ZIOCC/Zio-Qwiic-E-ink-Display-2.9ich/Black & White/firmware/Arduino/QWIICGDE029A1.h

/*******************
QWIICGDE029A1,h

*******************/

#ifndef _QWIICGDE029A1_h
#define _QWIICGDE029A1_h


#include"Arduino.h"
#include <Wire.h>

const unsigned char F8x16[]PROGMEM={
0xFF,0xFF,0xFF,0xFF,0xFF,0xFF,0xFF,0xFF,0xFF,0xFF,0xFF,0xFF,0xFF,0xFF,0xFF,0xFF,/*" ",32*/

0xFF,0xFF,0xFF,0xF7,0xF7,0xF7,0xF7,0xF7,0xF7,0xF7,0xFF,0xFF,0xF7,0xF7,0xFF,0xFF,/*"!",33*/

0xFF,0xB7,0xDB,0xDB,0xED,0xFF,0xFF,0xFF,0xFF,0xFF,0xFF,0xFF,0xFF,0xFF,0xFF,0xFF,/*""",34*/

0xFF,0xFF,0xFF,0xB7,0xB7,0xB7,0x81,0xDB,0xDB,0xDB,0x81,0xDB,0xDB,0xDB,0xFF,0xFF,/*"#",35*/

0xFF,0xFF,0xEF,0xC3,0xAD,0xAD,0xED,0xE3,0xCF,0xAF,0xAF,0xAD,0xAD,0xC3,0xEF,0xEF,/*"$",36*/

0xFF,0xFF,0xFF,0xDD,0xDA,0xEA,0xEA,0xF2,0xD5,0xA7,0xAB,0xAB,0xAD,0xDD,0xFF,0xFF,/*"%",37*/

0xFF,0xFF,0xFF,0xF3,0xED,0xED,0xED,0xF5,0x89,0xDA,0xD6,0xE6,0x6E,0x91,0xFF,0xFF,/*"&",38*/

0xFF,0xF9,0xFB,0xFB,0xFD,0xFF,0xFF,0xFF,0xFF,0xFF,0xFF,0xFF,0xFF,0xFF,0xFF,0xFF,/*"'",39*/

0xFF,0xBF,0xDF,0xEF,0xEF,0xF7,0xF7,0xF7,0xF7,0xF7,0xF7,0xEF,0xEF,0xDF,0xBF,0xFF,/*"(",40*/

0xFF,0xFD,0xFB,0xF7,0xF7,0xEF,0xEF,0xEF,0xEF,0xEF,0xEF,0xF7,0xF7,0xFB,0xFD,0xFF,/*")",41*/

0xFF,0xFF,0xFF,0xFF,0xF7,0xF7,0x94,0xE3,0xE3,0x94,0xF7,0xF7,0xFF,0xFF,0xFF,0xFF,/*"*",42*/

0xFF,0xFF,0xFF,0xFF,0xFF,0xEF,0xEF,0xEF,0x01,0xEF,0xEF,0xEF,0xFF,0xFF,0xFF,0xFF,/*"+",43*/

0xFF,0xFF,0xFF,0xFF,0xFF,0xFF,0xFF,0xFF,0xFF,0xFF,0xFF,0xFF,0xF9,0xFB,0xFB,0xFD,/*",",44*/

0xFF,0xFF,0xFF,0xFF,0xFF,0xFF,0xFF,0xFF,0x81,0xFF,0xFF,0xFF,0xFF,0xFF,0xFF,0xFF,/*"-",45*/

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

0xFF,0xFF,0xFF,0xFF,0xFF,0xFF,0xFF,0xFF,0xFF,0xFE,0x03,0xC1,0xFD,0xBF,0xFD,0xBF,/*"{",123*/

0xFF,0xFF,0xFF,0xFF,0xFF,0xFF,0xFF,0xFF,0x00,0x00,0xFF,0xFF,0xFF,0xFF,0xFF,0xFF,/*"|",124*/

0xFD,0xBF,0xFD,0xBF,0x03,0xC1,0xFF,0xFE,0xFF,0xFF,0xFF,0xFF,0xFF,0xFF,0xFF,0xFF,/*"}",125*/

0xFF,0xFF,0xFD,0xFF,0xFE,0xFF,0xFD,0xFF,0xFD,0xFF,0xFB,0xFF,0xFD,0xFF,0xFF,0xFF,/*"~",126*/	
	
};
class QWIICGDE029A1
{  
public:
void Full_Display(unsigned char *pic,unsigned char slave_addr);
void QWIICGDE029A1::Part_Display(unsigned char xStart,unsigned char xEnd,unsigned int yStart,unsigned int yEnd,unsigned char *DisBuffer,uint16_t part_buffer_size,unsigned char RamDataEntryMode,unsigned char slave_addr);
void EPD_Print_F16x8(unsigned char X, unsigned int Y, unsigned char len,char ch[],unsigned char slave_addr);
void EPD_Print_F8x16(unsigned char X, unsigned int Y, unsigned char len, char ch[], unsigned char slave_addr);
};

#endif
