ZIOCC/Zio-Qwiic-E-ink-Display-2.9ich/Black, White & Red/STM32/EPD_W21/Display_EPD_W21.h

#ifndef _DISPLAY_EPD_W21_H_
#define _DISPLAY_EPD_W21_H_



extern void driver_delay_us(unsigned int xus);
extern void driver_delay_xms(unsigned long xms);

extern void EPD_W21_WriteCMD(unsigned char command);
static void EPD_W21_Update(void);
static void EPD_W21_EnableChargepump(void);
static void EPD_W21_DisableChargepump(void);
static void EPD_W21_WirteLUT(unsigned char *LUTvalue);
static void EPD_W21_SetRamPointer(unsigned char addrX,unsigned char addrY,unsigned char addrY1);
static void EPD_W21_SetRamArea(unsigned char Xstart,unsigned char Xend,
						unsigned char Ystart,unsigned char Ystart1,unsigned char Yend,unsigned char Yend1);
static void EPD_W21_Write(unsigned char *value, unsigned char datalen);
static void EPD_W21_PowerOnSelfTest(void);
static void EPD_W21_PowerOnInit(void);

extern void EPD_W21_Init(void);
extern void EPD_W21_Test_Graphics(unsigned char PicNum);
extern void EPD_W21_UpdataDisplay(unsigned char *imgbuff);

#endif
/***********************************************************
						end file
***********************************************************/
